pascalguttmann/obat-powersupplysink/schematic/pss_schematic_0.14.5.pdf

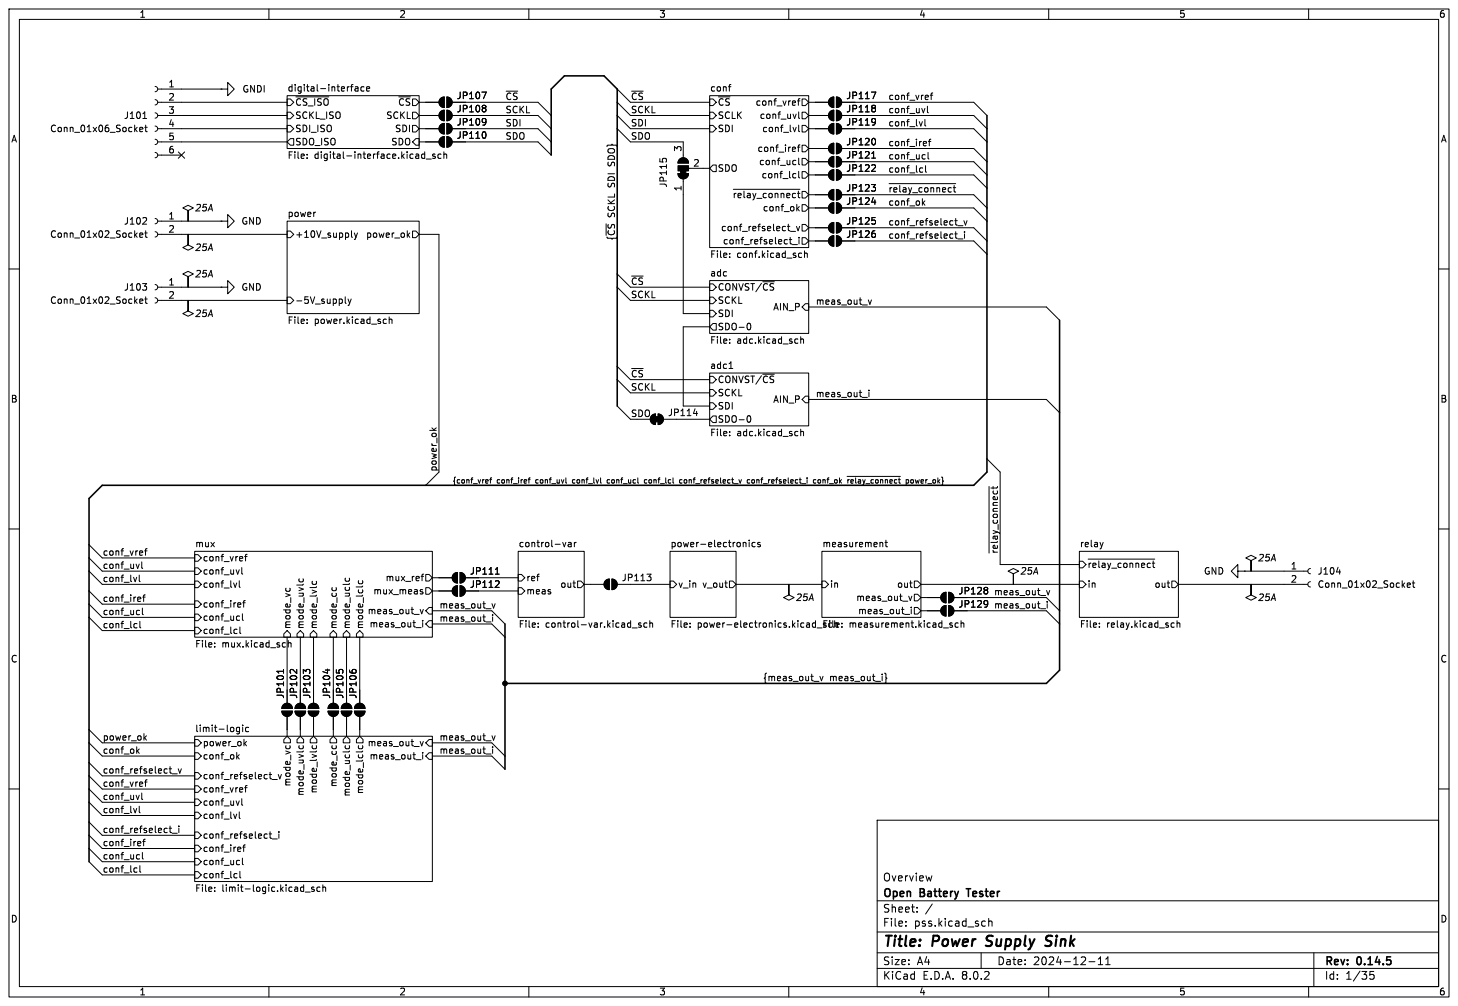
[picture p151: page 1]

~{CS_ISO} SDI_ISO
v_in v_out power-electronics File: power-electronics.kicad_sch AIN_P SDI CONVST/~{CS} SCKL SDO-0

~{CS} SCKL SDI SDO

limit-logic File: limit-logic.kicad_sch
meas_out_v meas_out_i conf_refselect_i conf_refselect_v

Id: 1/35 Title: Power Supply Sink


3 REFIO 4 REFGND 5 REFCAP 6 AIN_P 7 AIN_GND 8 ~{RST} 9 U201 ADS8665IPWR GND

1 SDI 10 CONVST/~{CS} 11 SCKL 12 SDO-0 13 ALARM/SDO-1/GPO 14 RVS 15 DVDD 16 AVDD

3 REFIO 4 REFGND 5 REFCAP 6 AIN_P 7 AIN_GND 8 ~{RST} 9 GND

Id: 2/35 Title: Power Supply Sink


3 REFIO 4 REFGND 5 REFCAP 6 AIN_P 7 AIN_GND 8 ~{RST} 9 U301 ADS8665IPWR

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

3 REFIO 4 REFGND 5 REFCAP 6 AIN_P 7 AIN_GND 8 ~{RST} 9 GND

Id: 3/35 Title: Power Supply Sink

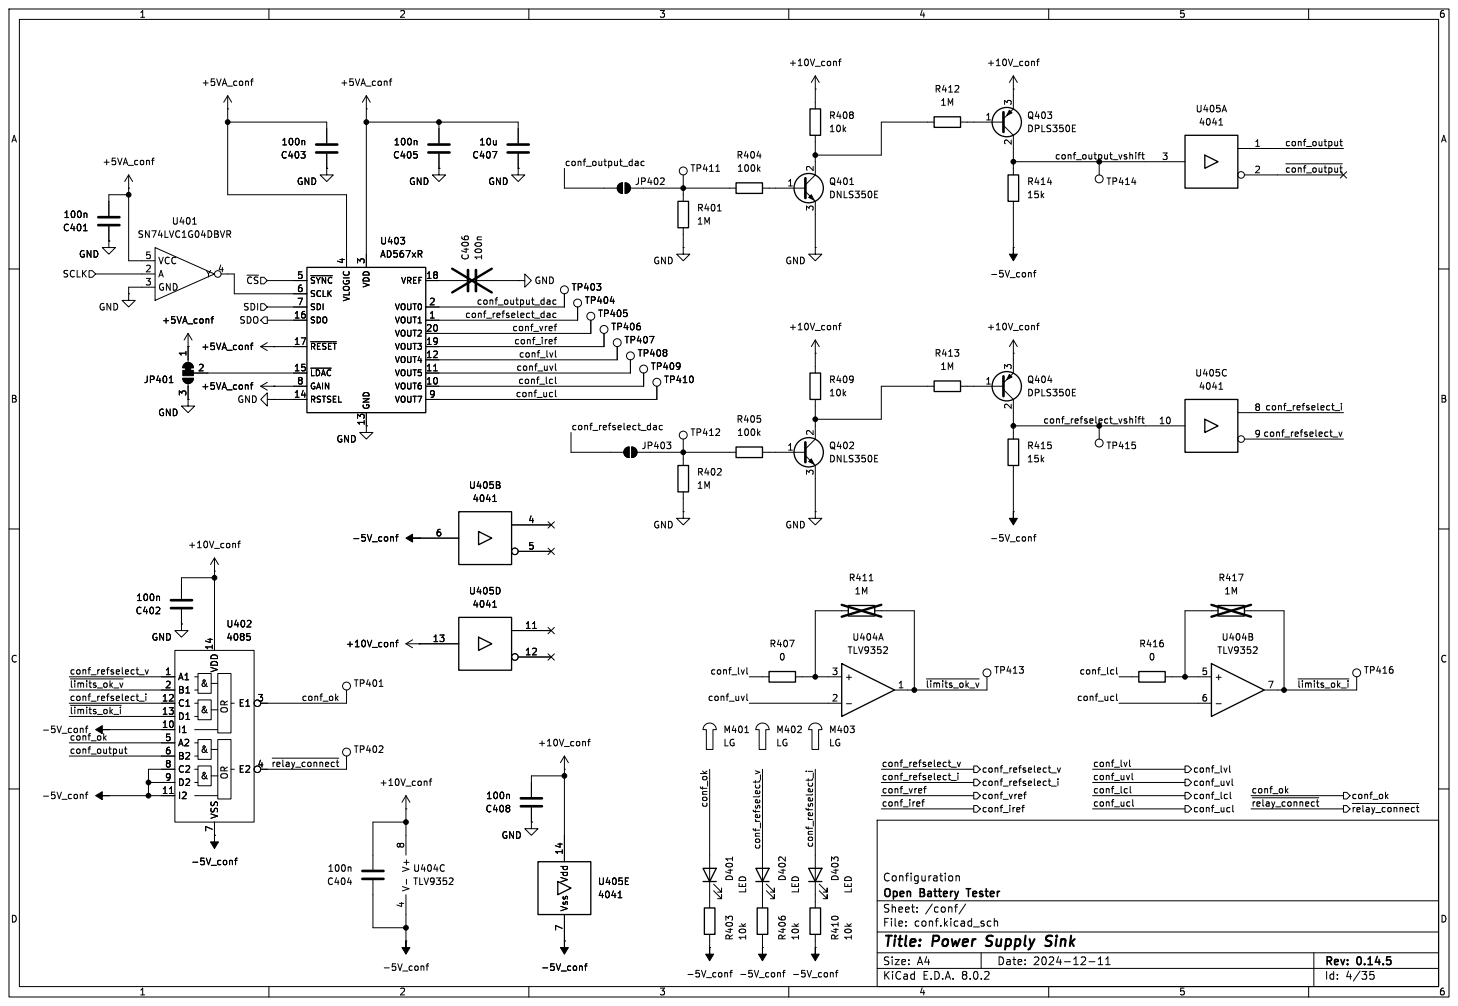
[picture p152: page 4]

Id: 4/35 Title: Power Supply Sink

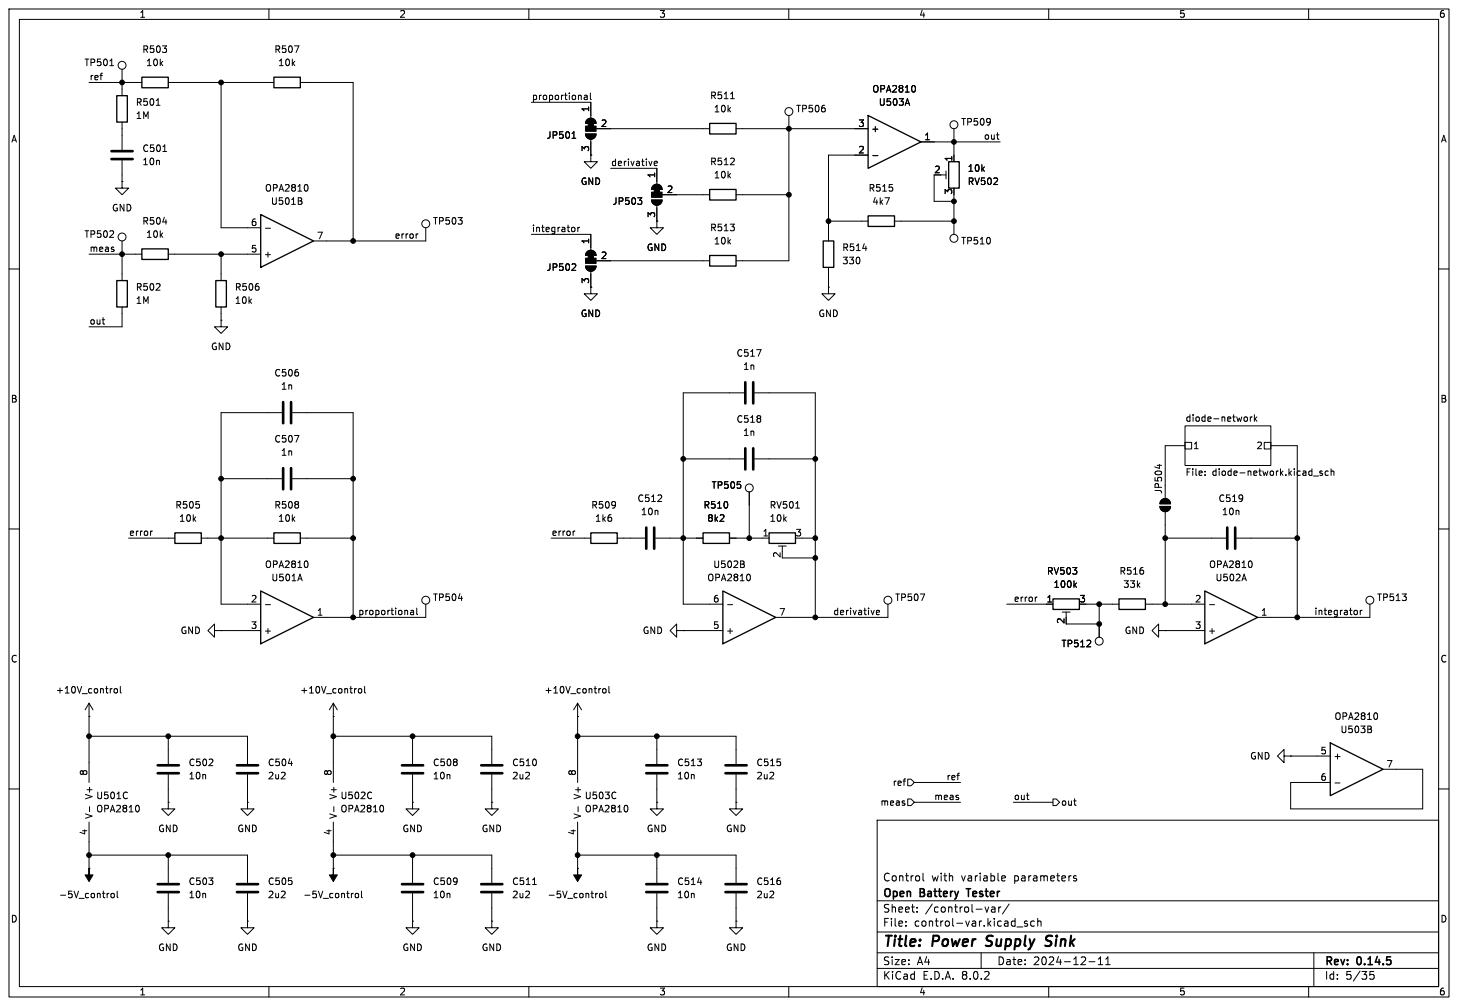
[picture p153: page 5]

diode-network File: diode-network.kicad_sch R510

Id: 5/35 Title: Power Supply Sink


Id: 6/35 Title: Power Supply Sink


File: digital-interface.kicad_sch Sheet: /digital-interface/
Id: 7/35 Title: Power Supply Sink

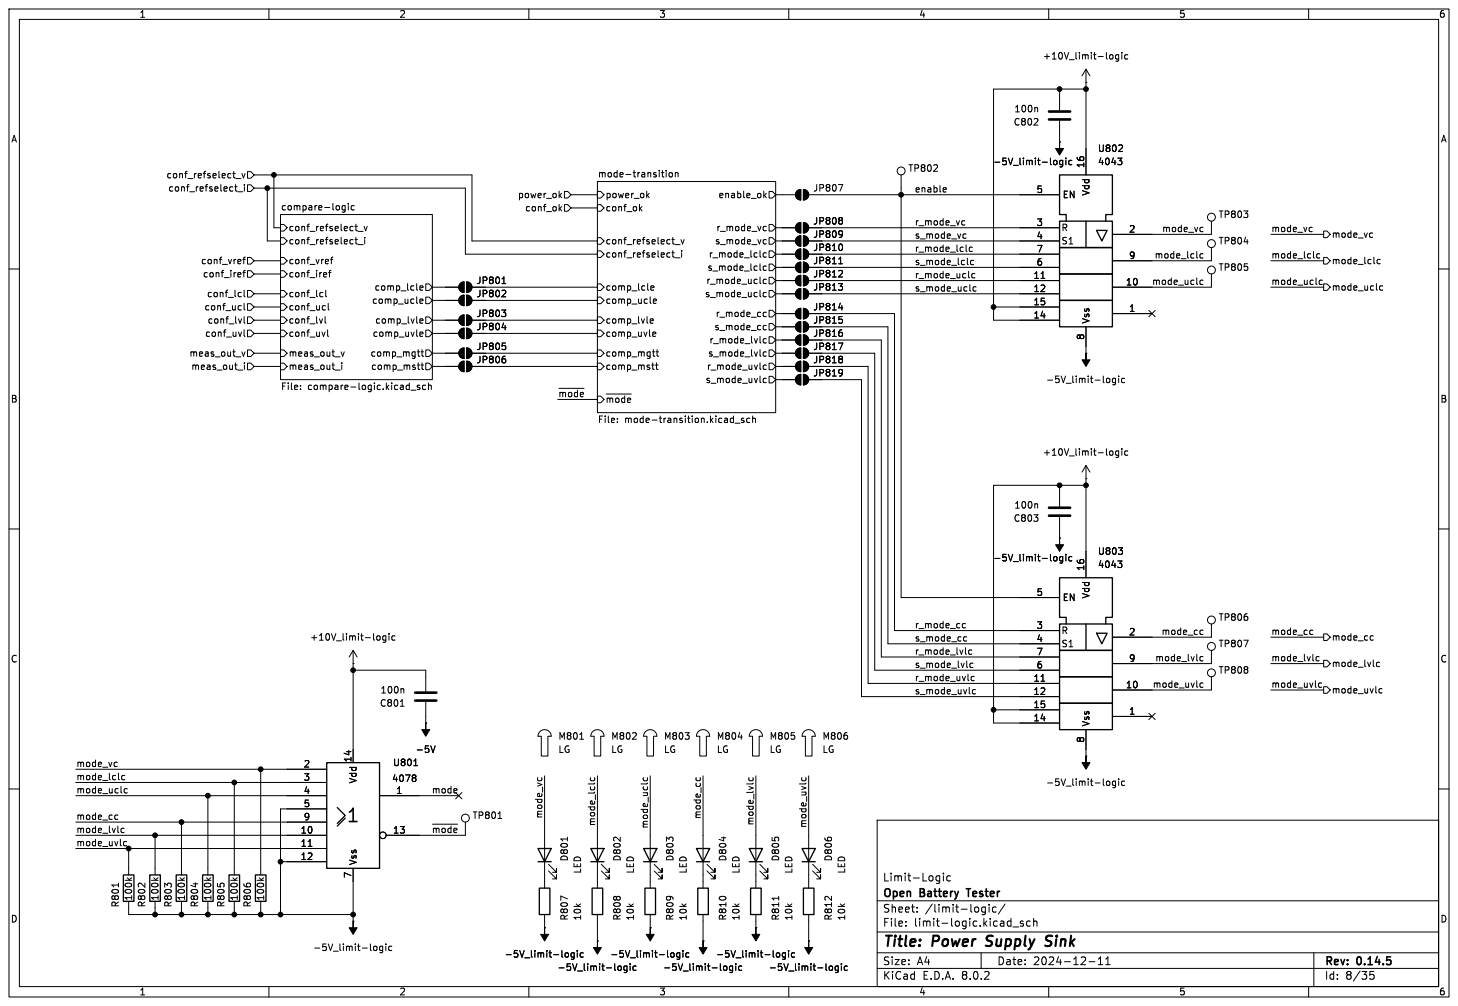
[picture p154: page 8]

conf_refselect_i comp_mgtt comp_mstt mode-transition File: mode-transition.kicad_sch

conf_refselect_i compare-logic File: compare-logic.kicad_sch

File: limit-logic.kicad_sch Sheet: /limit-logic/
Id: 8/35 Title: Power Supply Sink

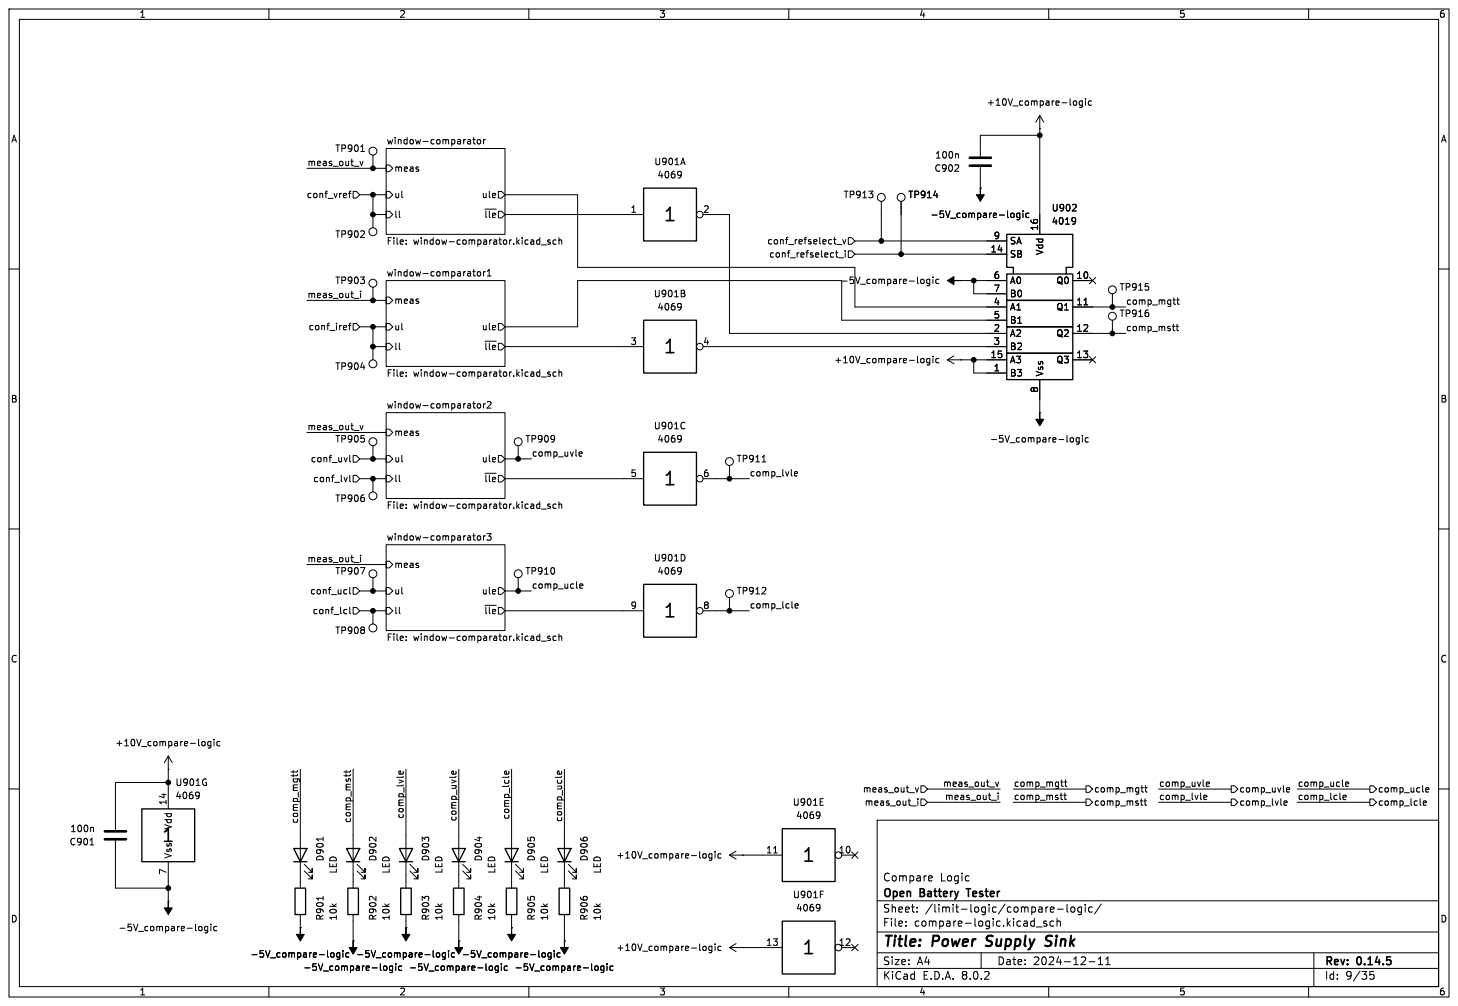
[picture p155: page 9]

llul window-comparator File: window-comparator.kicad_sch

llul window-comparator1 File: window-comparator.kicad_sch

llul window-comparator2 File: window-comparator.kicad_sch

llul window-comparator3 File: window-comparator.kicad_sch

File: compare-logic.kicad_sch Sheet: /limit-logic/compare-logic/
Id: 9/35 Title: Power Supply Sink

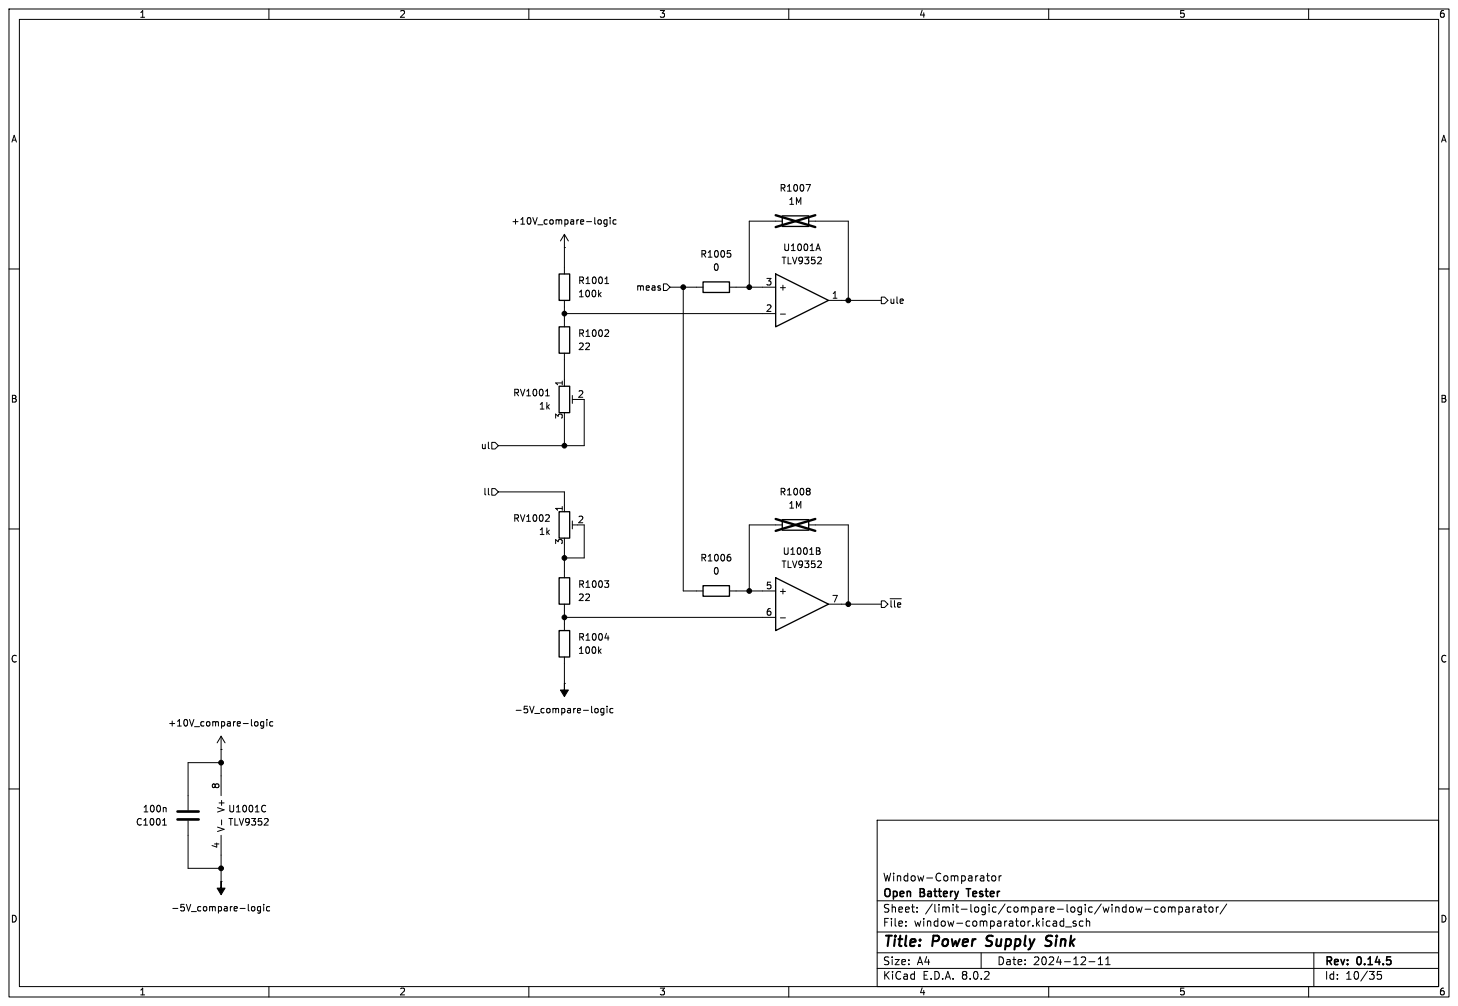
[picture p156: page 10]

File: window-comparator.kicad_sch Sheet: /limit-logic/compare-logic/window-comparator/
Id: 10/35 Title: Power Supply Sink

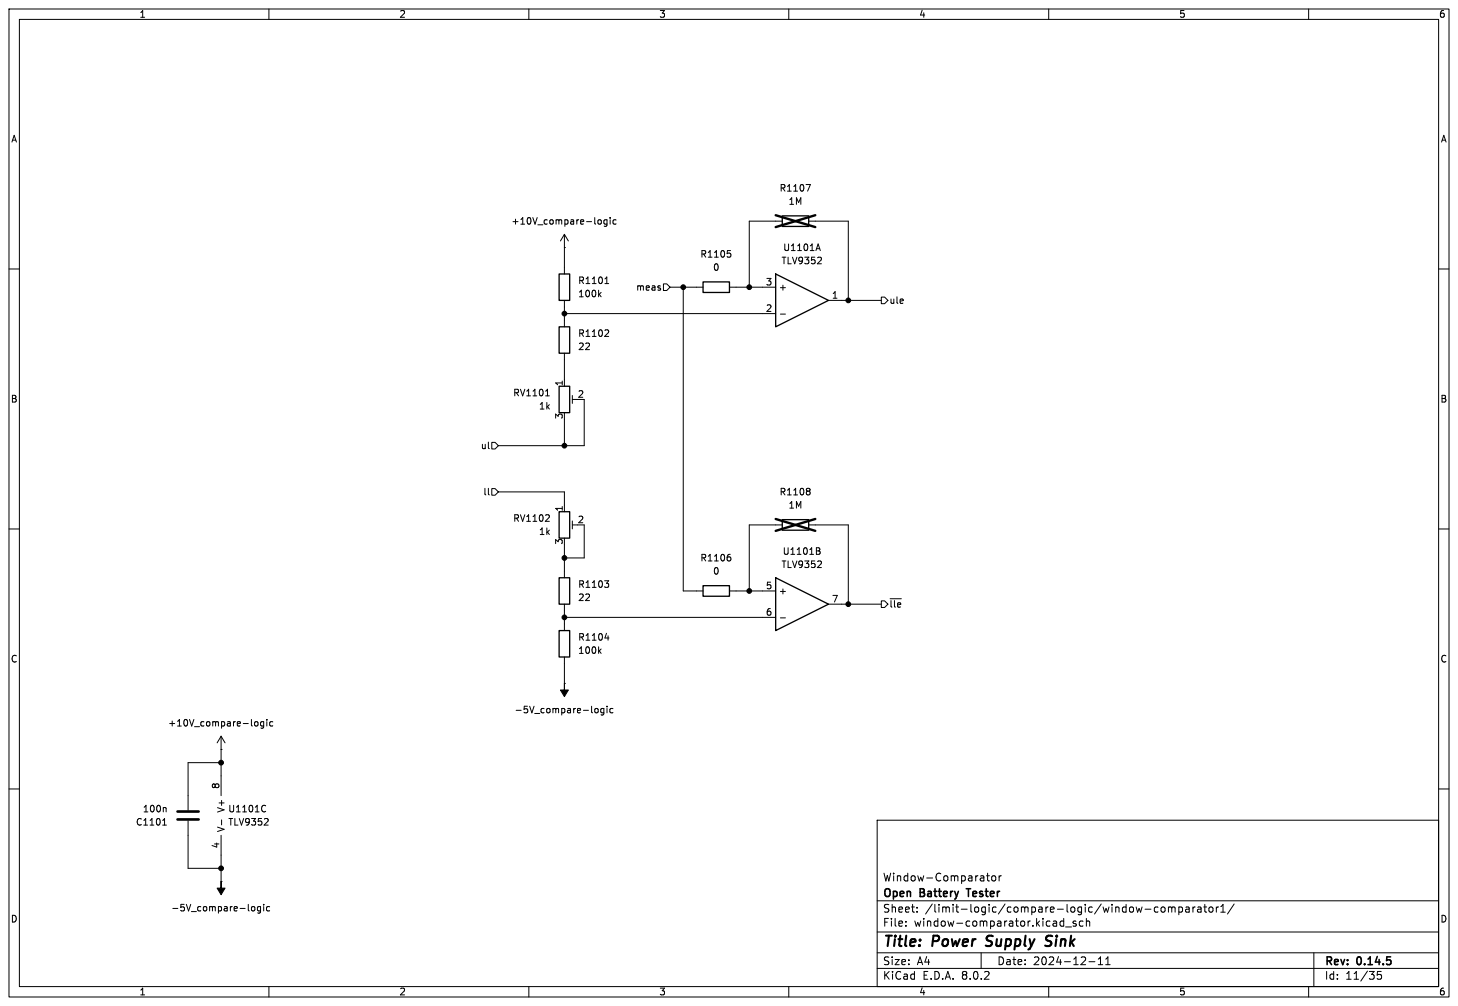
[picture p157: page 11]

File: window-comparator.kicad_sch Sheet: /limit-logic/compare-logic/window-comparator1/
Id: 11/35 Title: Power Supply Sink

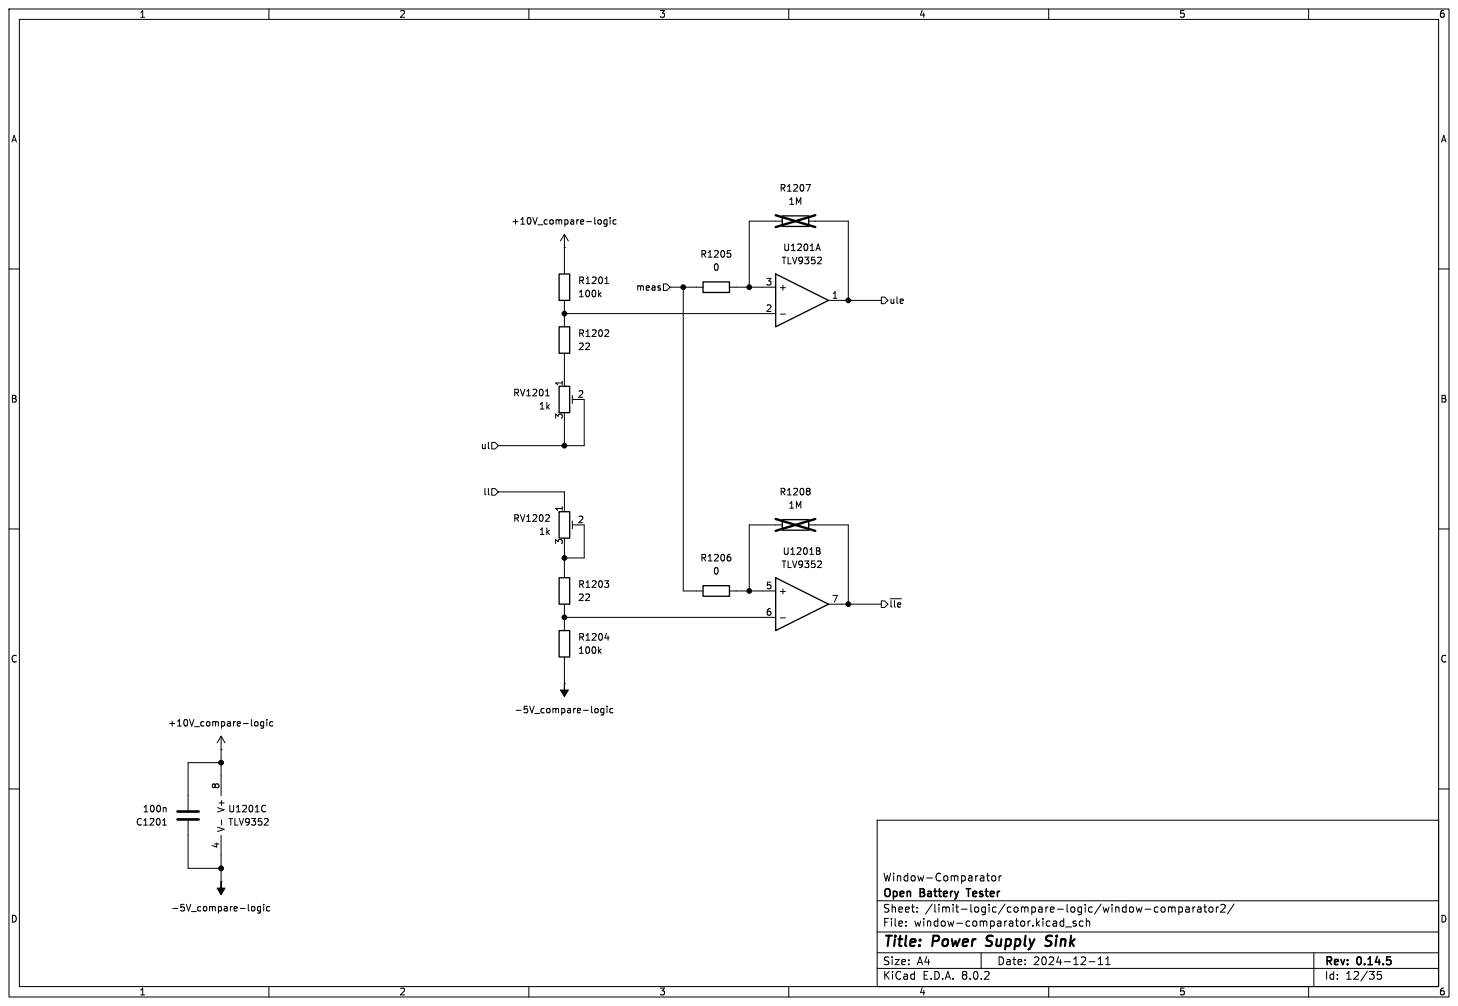
[picture p158: page 12]

File: window-comparator.kicad_sch Sheet: /limit-logic/compare-logic/window-comparator2/
Id: 12/35 Title: Power Supply Sink

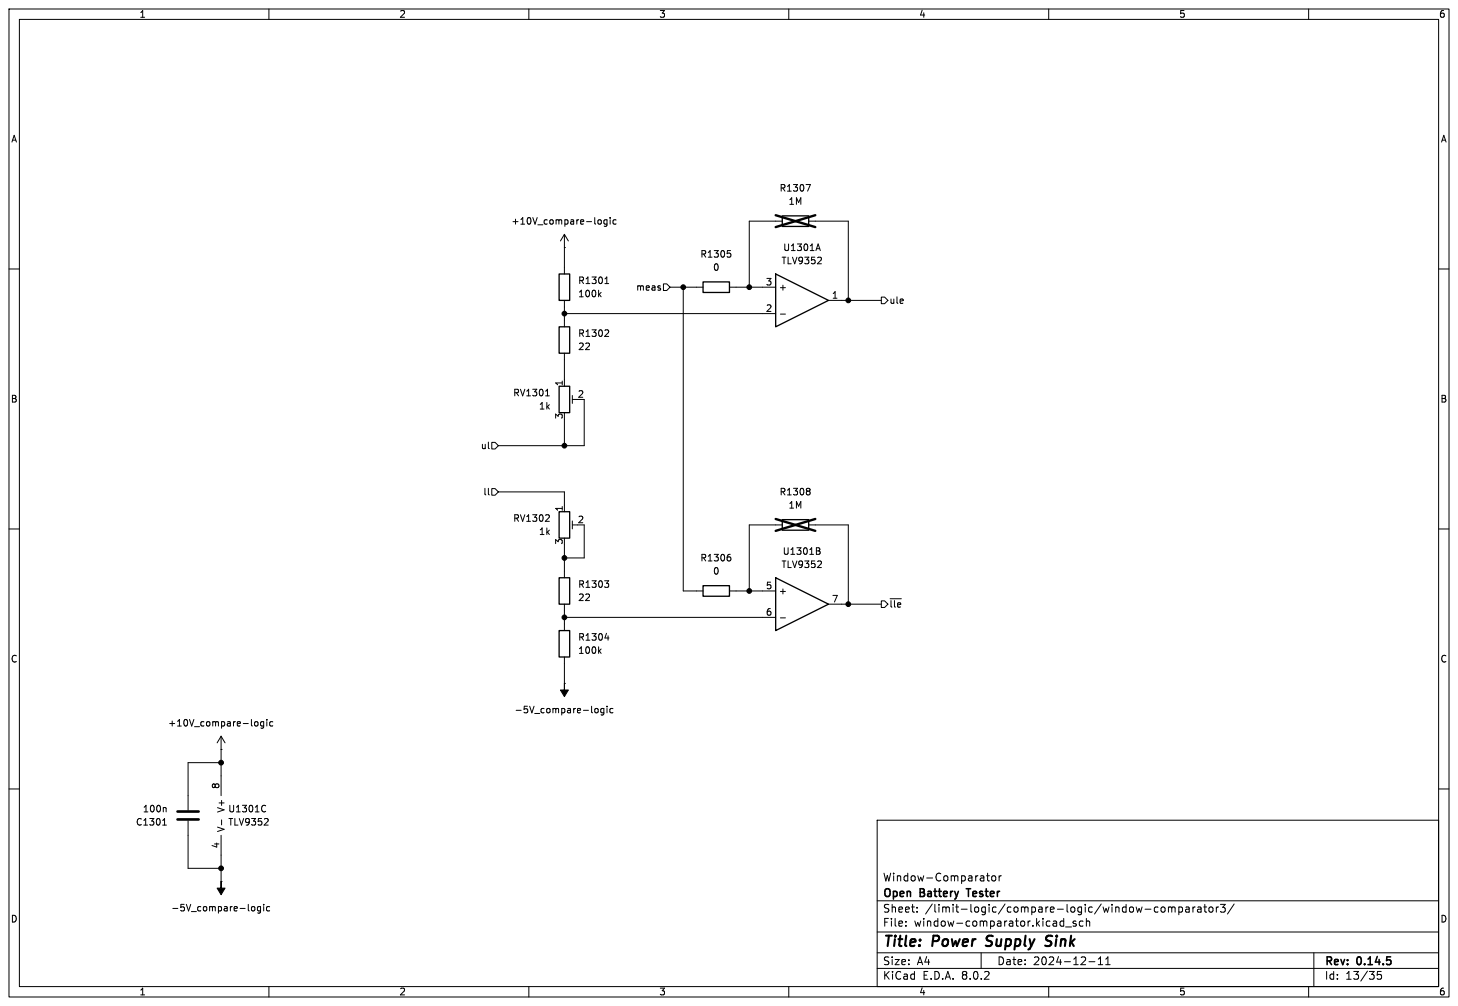
[picture p159: page 13]

File: window-comparator.kicad_sch Sheet: /limit-logic/compare-logic/window-comparator3/
Id: 13/35 Title: Power Supply Sink

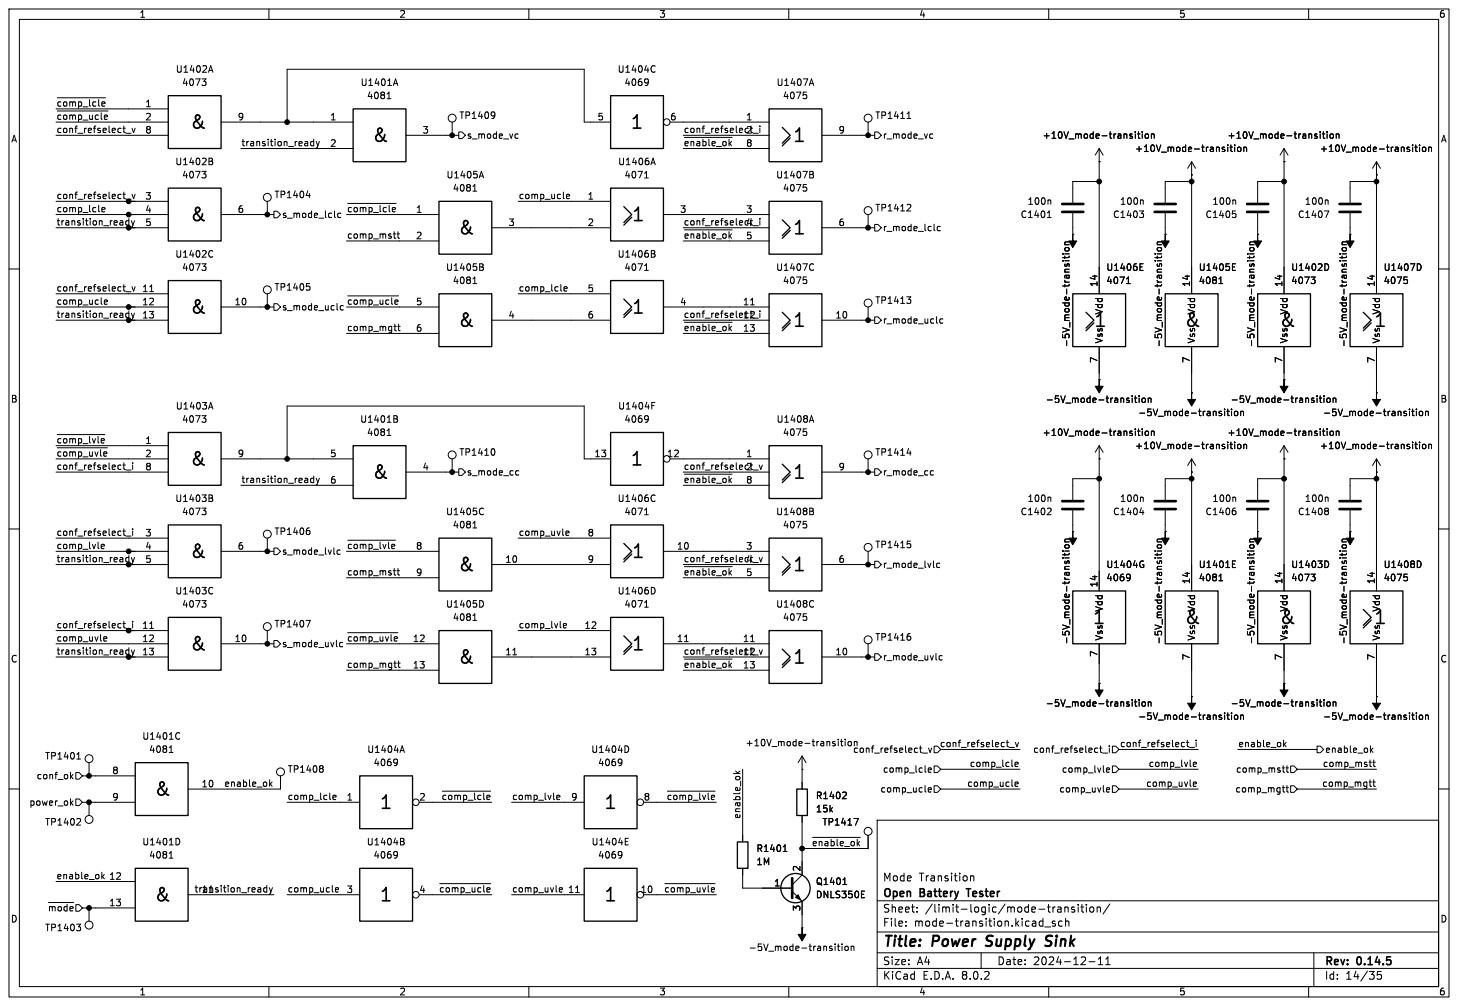
[picture p160: page 14]

File: mode-transition.kicad_sch Sheet: /limit-logic/mode-transition/
Id: 14/35 Title: Power Supply Sink

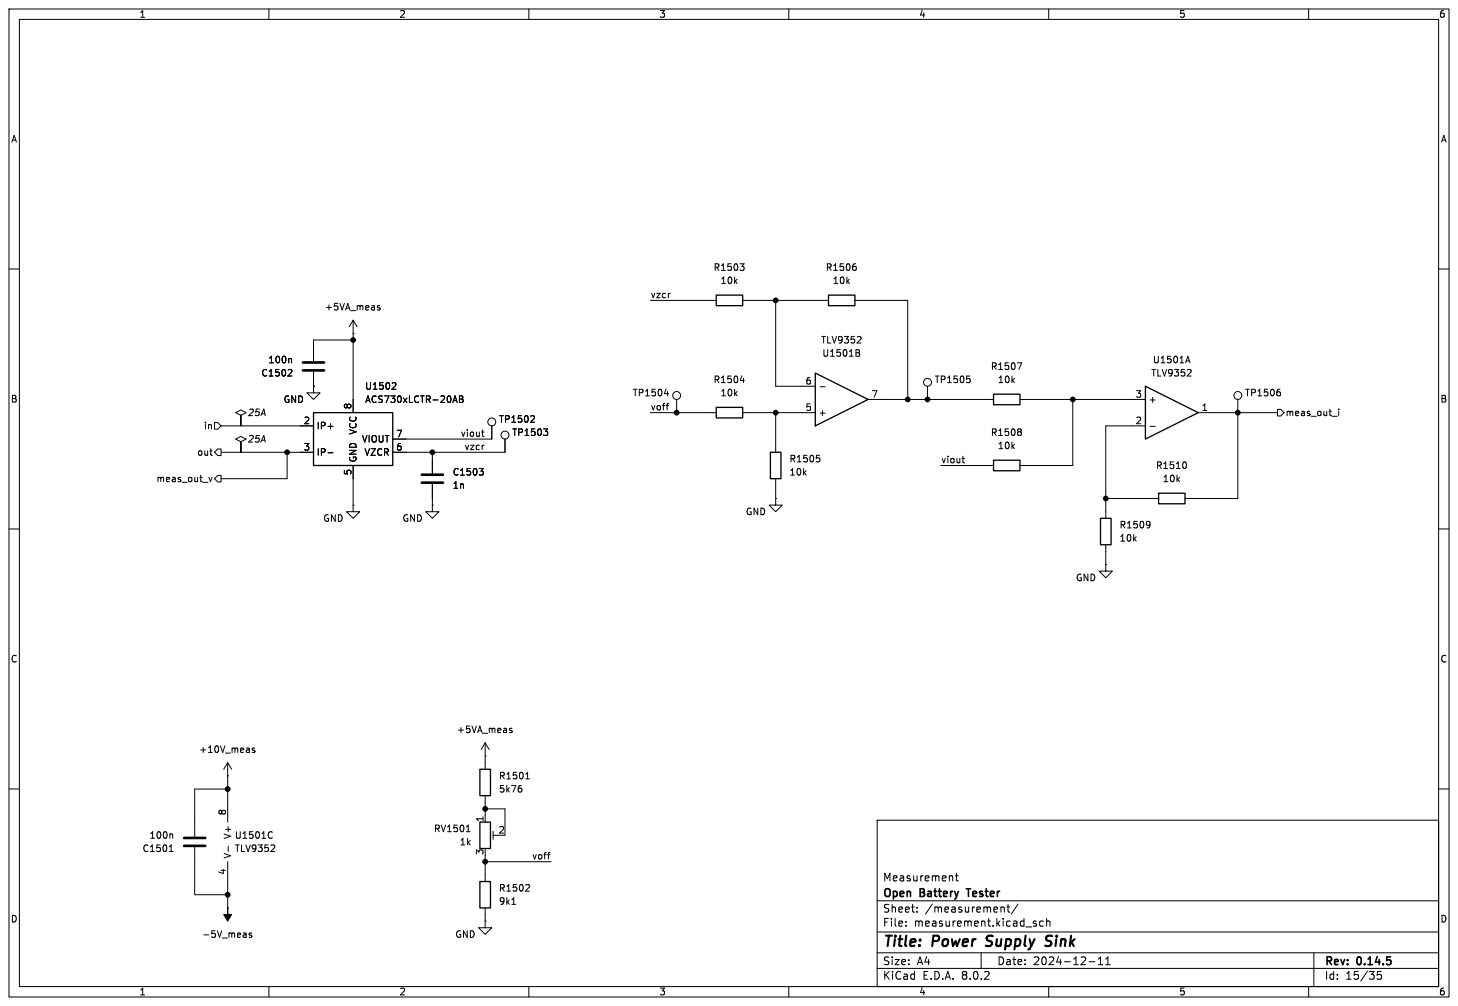
[picture p161: page 15]

Id: 15/35 Title: Power Supply Sink

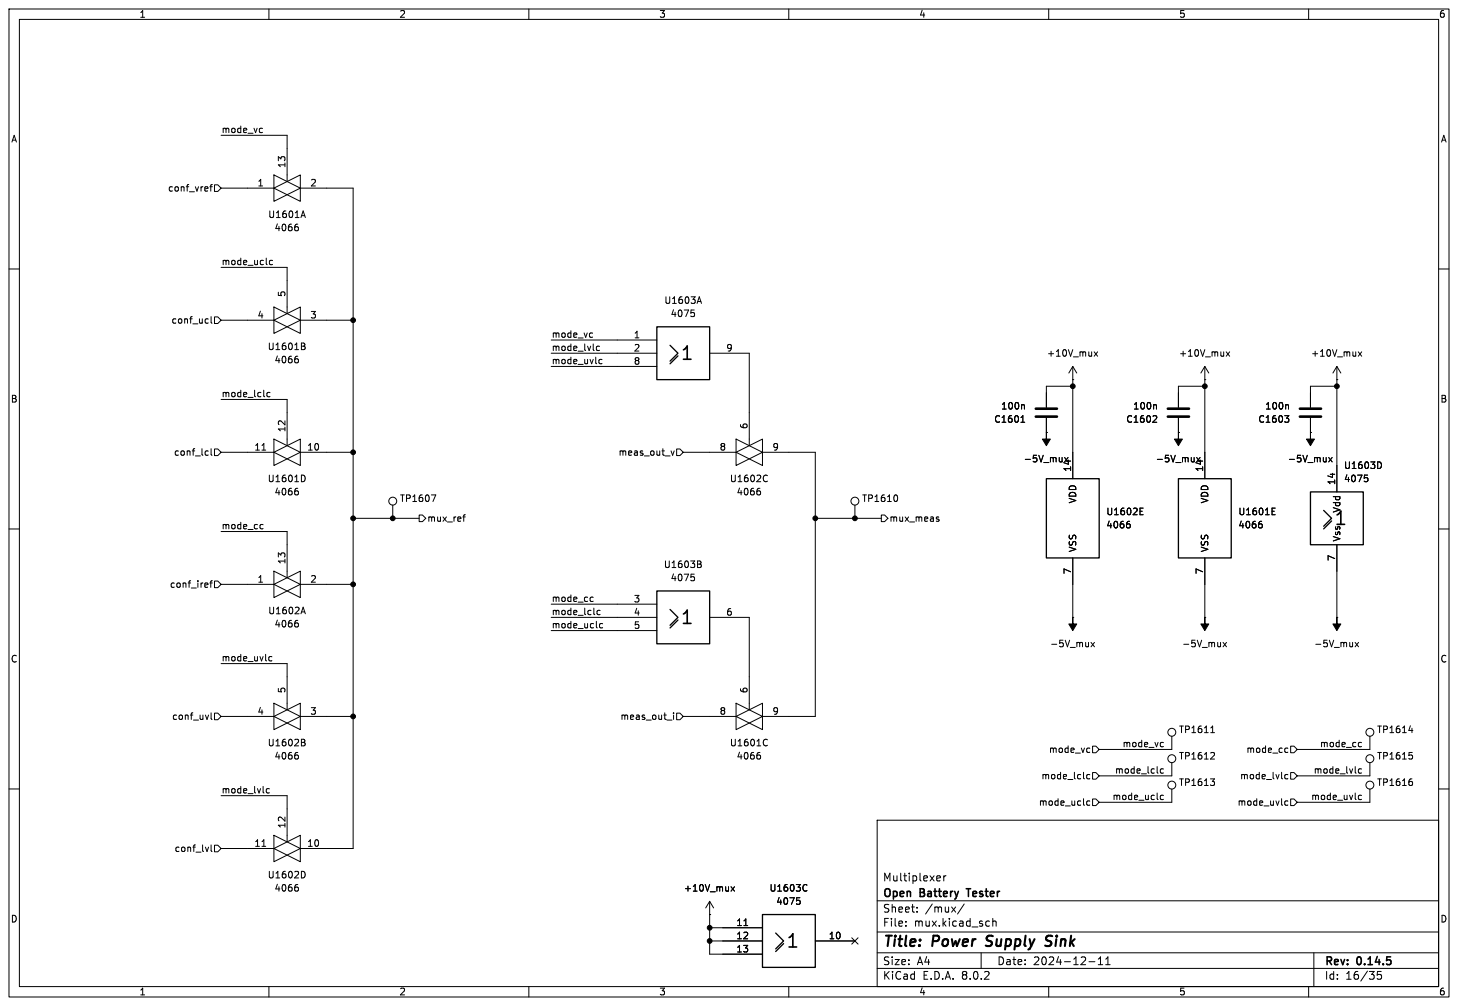
[picture p162: page 16]

Id: 16/35 Title: Power Supply Sink

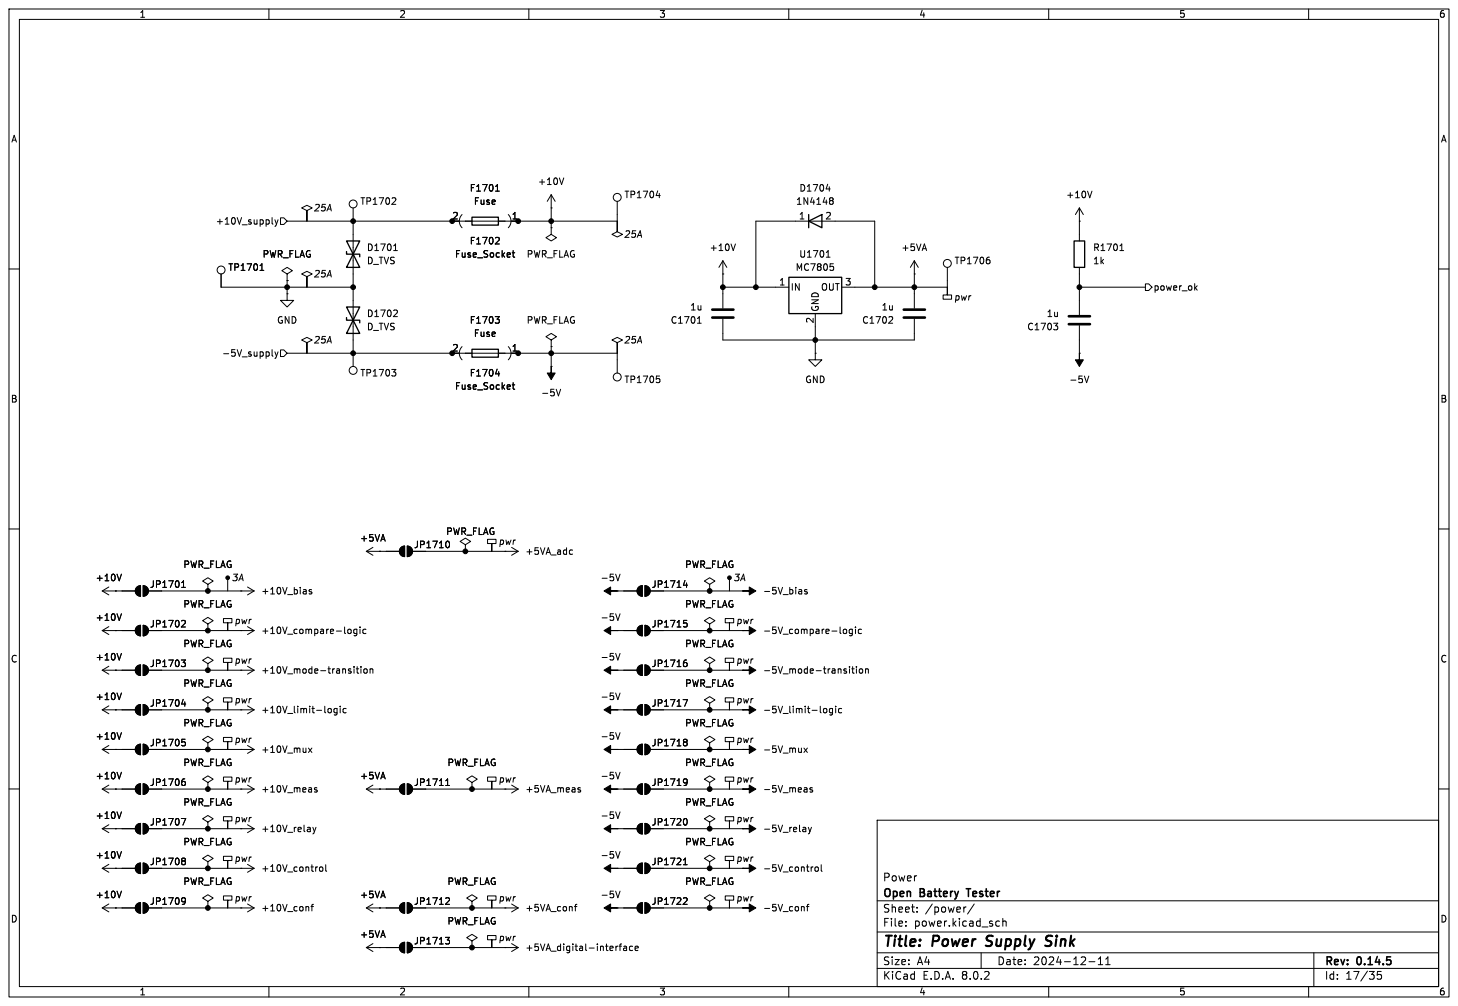
[picture p163: page 17]

File: power.kicad_sch Sheet: /power/
Id: 17/35 Title: Power Supply Sink


File: power-electronics.kicad_sch Sheet: /power-electronics/
Id: 18/35 Title: Power Supply Sink

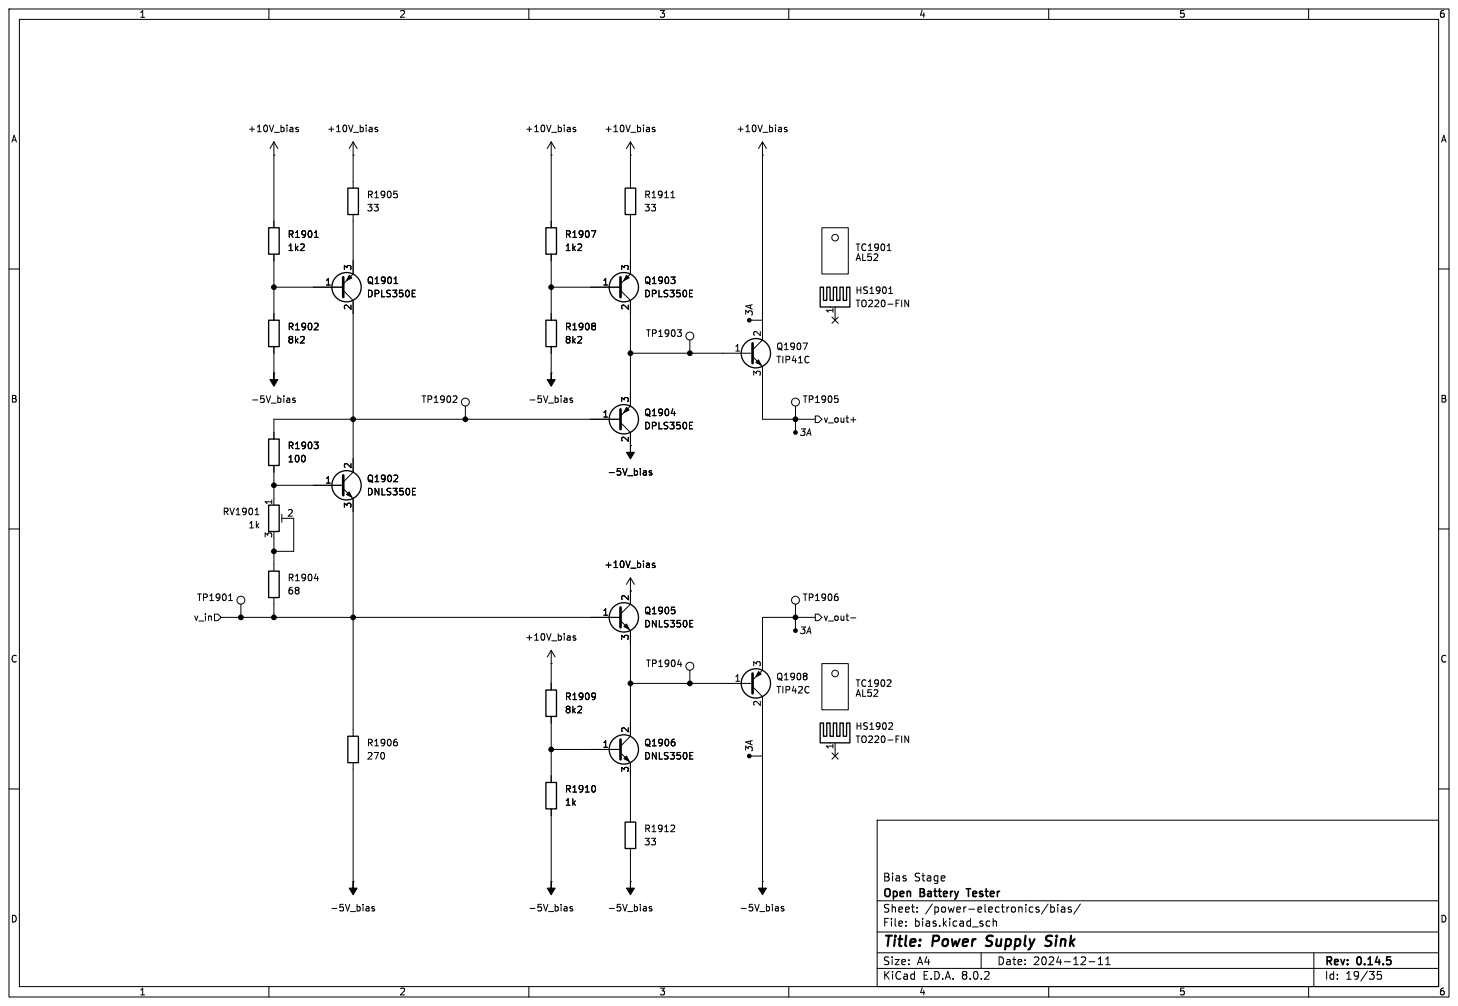
[picture p164: page 19]

File: bias.kicad_sch Sheet: /power-electronics/bias/
Id: 19/35 Title: Power Supply Sink


File: outstage.kicad_sch Sheet: /power-electronics/outstage/
Id: 20/35 Title: Power Supply Sink

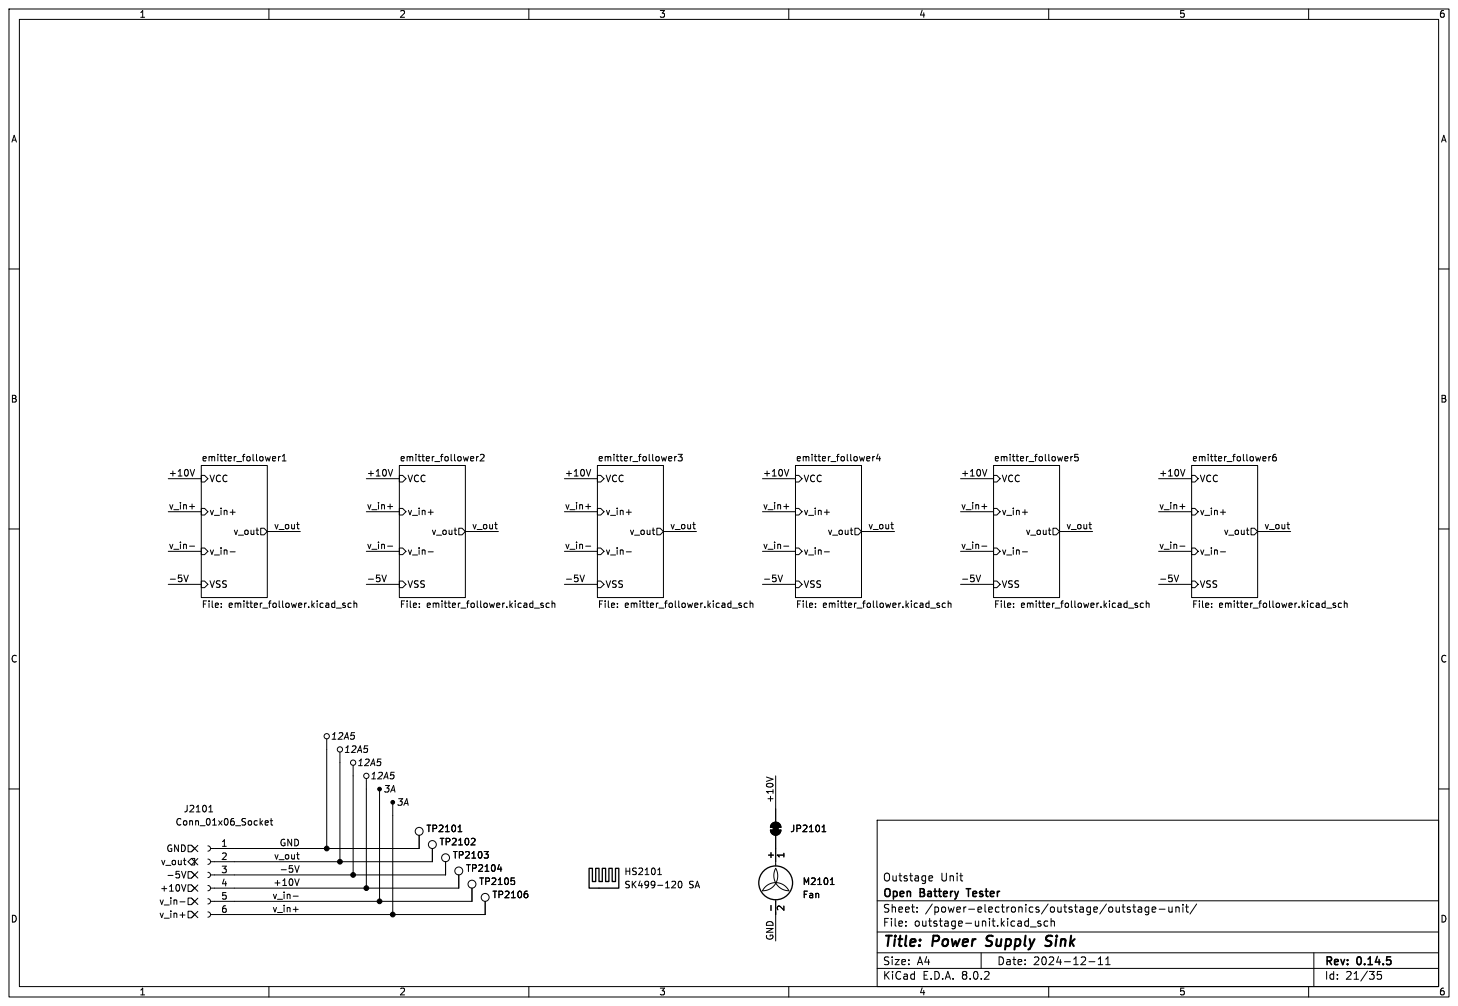
[picture p165: page 21]

File: outstage-unit.kicad_sch Sheet: /power-electronics/outstage/outstage-unit/
Id: 21/35 Title: Power Supply Sink


File: emitter_follower.kicad_sch Sheet: /power-electronics/outstage/outstage-unit/emitter_follower1/
Id: 22/35 Title: Power Supply Sink


File: emitter_follower.kicad_sch Sheet: /power-electronics/outstage/outstage-unit/emitter_follower2/
Id: 23/35 Title: Power Supply Sink


File: emitter_follower.kicad_sch Sheet: /power-electronics/outstage/outstage-unit/emitter_follower3/
Id: 24/35 Title: Power Supply Sink


File: emitter_follower.kicad_sch Sheet: /power-electronics/outstage/outstage-unit/emitter_follower4/
Id: 25/35 Title: Power Supply Sink


File: emitter_follower.kicad_sch Sheet: /power-electronics/outstage/outstage-unit/emitter_follower5/
Id: 26/35 Title: Power Supply Sink


File: emitter_follower.kicad_sch Sheet: /power-electronics/outstage/outstage-unit/emitter_follower6/
Id: 27/35 Title: Power Supply Sink

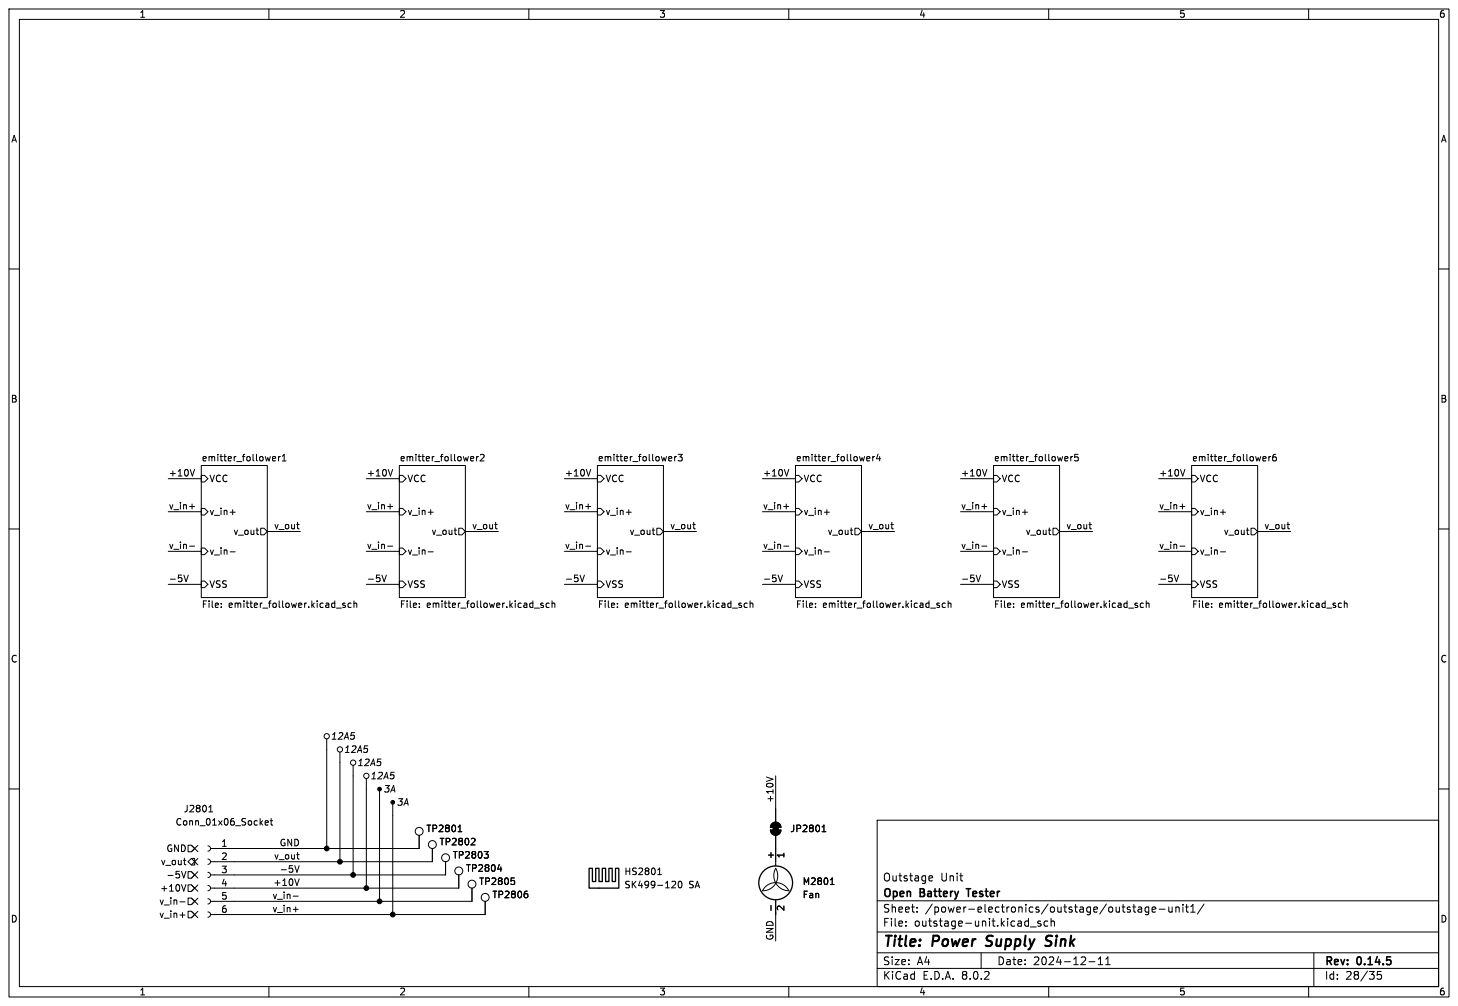
[picture p166: page 28]

File: outstage-unit.kicad_sch Sheet: /power-electronics/outstage/outstage-unit1/
Id: 28/35 Title: Power Supply Sink


File: emitter_follower.kicad_sch Sheet: /power-electronics/outstage/outstage-unit1/emitter_follower1/
Id: 29/35 Title: Power Supply Sink


File: emitter_follower.kicad_sch Sheet: /power-electronics/outstage/outstage-unit1/emitter_follower2/
Id: 30/35 Title: Power Supply Sink


File: emitter_follower.kicad_sch Sheet: /power-electronics/outstage/outstage-unit1/emitter_follower3/
Id: 31/35 Title: Power Supply Sink


File: emitter_follower.kicad_sch Sheet: /power-electronics/outstage/outstage-unit1/emitter_follower4/
Id: 32/35 Title: Power Supply Sink


File: emitter_follower.kicad_sch Sheet: /power-electronics/outstage/outstage-unit1/emitter_follower5/
Id: 33/35 Title: Power Supply Sink


File: emitter_follower.kicad_sch Sheet: /power-electronics/outstage/outstage-unit1/emitter_follower6/
Id: 34/35 Title: Power Supply Sink


File: relay.kicad_sch Sheet: /relay/
Id: 35/35 Title: Power Supply Sink
