pascalguttmann/obat-powersupplysink/board/brd-1.0.0/pss-B_Cu.pdf

Id: 1/1 Title: Power Supply Sink
