pascalguttmann/obat-powersupplysink/board/brd-1.0.0/pss-F_Mask.pdf

Id: 1/1 Title: Power Supply Sink
