pascalguttmann/obat-powersupplysink/board/brd-0.14.0/pss-F_Mask.pdf

Id: 1/1 Title: Power Supply Sink
