pascalguttmann/obat-powersupplysink/board/brd-0.13.0/pss-F_Silkscreen.pdf

Id: 1/1 Title: Power Supply Sink
