pascalguttmann/obat-powersupplysink/board/brd-0.12.0/pss-F_Paste.pdf

Id: 1/1 Title: Power Supply Sink
